jasepellerin/Unit-01/ergogen/test/outlines/circles___outlines_outline_dxf.dxf

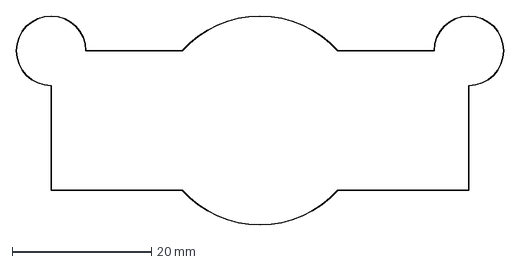
[picture p19: CAD file, 2022-04-10]
ergogen/test/outlines/circles___outlines_outline_dxf.dxf
70.0 x 30.0 mm
