jasepellerin/Unit-01/ergogen/test/outlines/basic___outlines_outline_dxf.dxf

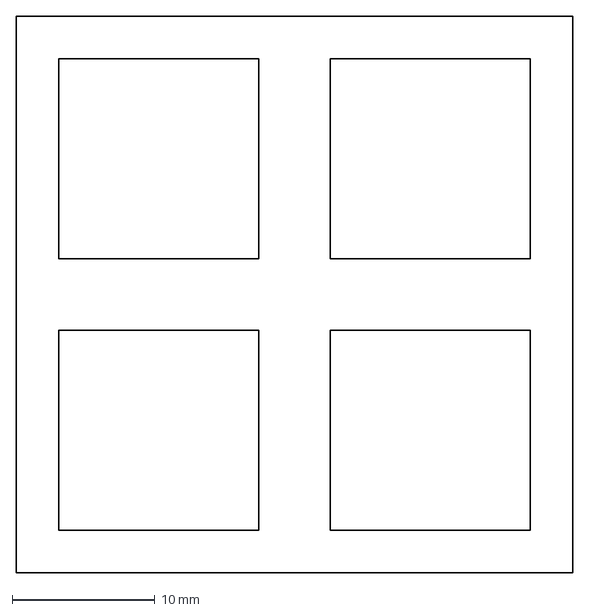
[picture p20: CAD file, 2022-04-10]
ergogen/test/outlines/basic___outlines_outline_dxf.dxf
39.0 x 39.0 mm
