jasepellerin/Unit-01/ergogen/test/outlines/gluing___outlines_optout_dxf.dxf

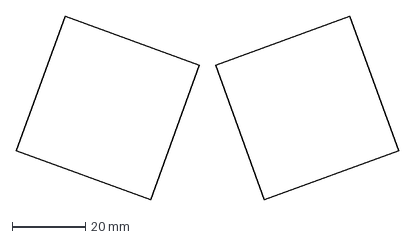
[picture p21: CAD file, 2022-04-10]
ergogen/test/outlines/gluing___outlines_optout_dxf.dxf
104.3 x 50.0 mm
