jasepellerin/Unit-01/ergogen/test/outlines/affect_mirror___outlines_test_dxf.dxf

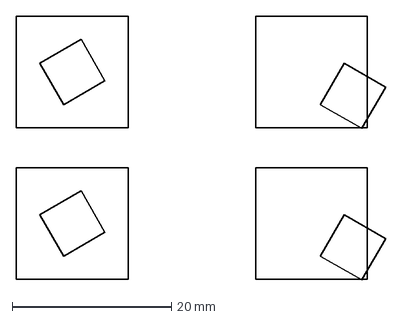
[picture p22: CAD file, 2022-04-10]
ergogen/test/outlines/affect_mirror___outlines_test_dxf.dxf
46.3 x 33.1 mm
