jasepellerin/Unit-01/ergogen/test/outlines/gluing___outlines_outline_dxf.dxf

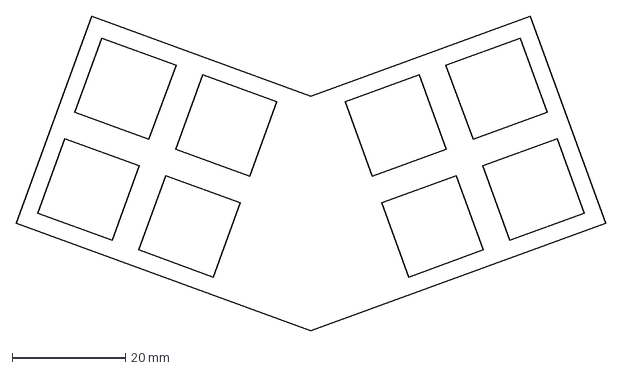
[picture p23: CAD file, 2022-04-10]
ergogen/test/outlines/gluing___outlines_outline_dxf.dxf
104.3 x 55.6 mm
